dj8111/RetroWatch-S3/3d_models/rear_case.scad

// ==============================================================================
// RetroWatch-S3 單獨後蓋 (Rear Case) 3D 模型原始碼
// ==============================================================================
view_mode = "rear_only";
include <generate_models.scad>
